Tahitibob35/roller-shutter/src/prefs.cpp

#include "prefs.h"
#include "prgm.h"

Preferences preferences;

char buffer[PRGM_COUNT * sizeof(prgm_t)];
prgm_t *prgms = (prgm_t *) buffer;

void prefs_set_key(String key) {
  
  Serial.println("PREFS - Storing key");
  preferences.begin("application",false);
  preferences.putString("key", key);
  preferences.end();
  
}


void prefs_get_key(char * key) {
  
  Serial.print("PREFS - Reading key : ");
  preferences.begin("application",false);
  preferences.getString("key").toCharArray(key, KEY_LENGTH);
  Serial.println(key);
  preferences.end();
    
}

void prefs_set_token(String token) {
  
  Serial.println("PREFS - Storing token");
  preferences.begin("token",false);
  preferences.putString("token", token);
  preferences.end();
  
}


void prefs_get_token(char * token) {
  
  Serial.print("PREFS - Reading token : ");
  preferences.begin("token",false);
  preferences.getString("token").toCharArray(token, 16);
  Serial.println(token);
  preferences.end();
    
}

void prefs_set_syslog_state(boolean syslog_state) {
  
  Serial.println("PREFS - Storing syslog state: " + syslog_state ? "true" : "false");
  preferences.begin("syslog",false);
  preferences.putBool("syslog_state", syslog_state);
  preferences.end();
  
}


boolean prefs_get_syslog_state() {
  boolean syslog_state = false;

  Serial.print("PREFS - Reading syslog state : ");
  preferences.begin("syslog",false);
  syslog_state = preferences.getBool("syslog_state");
  preferences.end();
  
  if (syslog_state)
  {
    Serial.println("enabled");
  }
  else
  {
    Serial.println("disabled");
  }
  return syslog_state; 
}


void prefs_set_syslog_ip(String syslog_ip) {
  
  Serial.println("PREFS - Storing syslog ip");
  preferences.begin("syslog",false);
  preferences.putString("syslog_ip", syslog_ip);
  preferences.end();
  
}


void prefs_get_syslog_ip(char * syslog_ip) {
  
  Serial.print("PREFS - Reading syslog_ip : ");
  preferences.begin("syslog",false);
  preferences.getString("syslog_ip").toCharArray(syslog_ip, IP_LENGTH);
  Serial.println(syslog_ip);
  preferences.end();
  
}

void prefs_set_syslog_port(int syslog_port) {
  
  Serial.println("PREFS - Storing syslog port");
  preferences.begin("syslog",false);
  preferences.putUShort("syslog_port", syslog_port);
  preferences.end();
  
}


uint16_t prefs_get_syslog_port() {
  uint16_t value=-1;

  Serial.print("PREFS - Reading syslog_port : ");
  preferences.begin("syslog",false);
  value = preferences.getUShort("syslog_port");

  Serial.println(value);
  preferences.end();

  return value;  
}


void prefs_set_ntp_server(String ntp_server) {
  
  Serial.println("PREFS - Storing ntp server url");
  preferences.begin("ntp",false);
  preferences.putString("ntp_server", ntp_server);
  preferences.end();
  
}


void prefs_get_ntp_server(char * ntp_server) {
  
  Serial.print("PREFS - Reading ntp server url : ");
  preferences.begin("ntp",false);
  preferences.getString("ntp_server").toCharArray(ntp_server, NTP_SERVER_LENGTH);
  if(ntp_server == NULL || strlen(ntp_server) == 0 || ntp_server[0] == '\0'){
    String("pool.ntp.org").toCharArray(ntp_server, NTP_SERVER_LENGTH);
  }
  Serial.println(ntp_server);
  preferences.end();
  
}

void prefs_set_accesspoint(String accesspoint) {
  
  Serial.println("PREFS - Storing accesspoint");
  preferences.begin("wifi",false);
  preferences.putString("accesspoint", accesspoint);
  preferences.end();
  
}


void prefs_get_accesspoint(char * accesspoint) {
  
  Serial.print("PREFS - Reading accesspoint : ");
  preferences.begin("wifi",false);
  preferences.getString("accesspoint").toCharArray(accesspoint, ACCESSPOINT_LENGTH);
  Serial.println(accesspoint);
  preferences.end();
  
}


void prefs_set_password(String password) {
  
  Serial.println("PREFS - Storing password");
  preferences.begin("wifi",false);
  preferences.putString("password", password);
  preferences.end();
  
}


void prefs_get_password(char * password) {
  
  Serial.print("PREFS - Reading password : ");
  preferences.begin("wifi",false);
  preferences.getString("password").toCharArray(password, PASSWORD_LENGTH);
  Serial.println(password);
  preferences.end();
  
}


uint16_t prefs_get_prgmcount() {

  uint16_t value = 0;
  
  Serial.print("PREFS - Reading prgmcount : ");
  preferences.begin("prgms",false);
  value = preferences.getUShort("prgmcount");
  Serial.println(value);
  preferences.end();

  return value;
  
}


void prefs_set_prgmcount(int prgmcount) {
  
  Serial.println("PREFS - Storing prgmcount");
  preferences.begin("prgms",false);
  preferences.putUShort("prgmcount", prgmcount);
  preferences.end();
  
}


void prefs_loadprgms() {
  
  Serial.println("PREFS - loadprgms");
  preferences.begin("prgms",false);

  size_t prgms_length = preferences.getBytesLength("prgms");

  Serial.print("PREFS - loadprgms - Size in memory :");
  Serial.println(prgms_length);

  if (prgms_length != PRGM_COUNT * sizeof(prgm_t)) { // simple check that data fits
    Serial.println("PRGM - loadprgms - Memory invalid or empty, cleaning");
    preferences.putBytes("prgms", prgms, PRGM_COUNT * sizeof(prgm_t));
  }
  
  preferences.getBytes("prgms", buffer, prgms_length);
  Serial.println("PREFS - loadprgms - Data loaded");

  preferences.end();
}


void prefs_storeprgms() {
  
  Serial.println("PREFS - storeprgms");
  preferences.begin("prgms",false);
  preferences.putBytes("prgms", prgms, PRGM_COUNT * sizeof(prgm_t));
  preferences.end();
}
