Tahitibob35/roller-shutter/src/vars-david.h

#ifndef VARS_H_
#define VARS_H_

#define delay_after_move

#define REMOTES_COUNT 3

const char *remote_name[REMOTES_COUNT] = { 
  (char *)"Cuisine", 
  (char *)"Salon",
  (char *)"Salle &agrave; M.",
};

#endif /* VARS_H_ */
