Tahitibob35/roller-shutter/src/vars-olivier.h

#ifndef VARS_H_
#define VARS_H_

#define REMOTES_COUNT 10

const char *remote_name[REMOTES_COUNT] = { 
  (char *)"Cuisine", 
  (char *)"Baie vitr&eacute;e",
  (char *)"Buffet",
  (char *)"Porte fen&ecirc;tre",
  (char *)"Bureau",
  (char *)"Chambre 1",
  (char *)"Chambre 2",
  (char *)"Chambre 3",
  (char *)"Tout bas",
  (char *)"Tout haut",
};

#endif /* VARS_H_ */
